XiangpengLiang/Gesture-Interface/guessing.cpp

//#include "window.h"
#include"guessing.h"
#include <QDebug>


guessing::guessing()
{
    paper.load(":/image/paper.png");
    scissor.load(":/image/scissor.png");
    rock.load(":/image/rock.png");
    dog.load(":/image/dog.png");
    boom.load(":/image/boom.png");

    Quit= new QPushButton("Quit", this);
    connect(Quit, SIGNAL (released()), this, SLOT (handleButton()));

}


void guessing::paintEvent(QPaintEvent *)  //Change the picture
{

    QPainter painter(this);


    uint8_t result = Compare[0]<<4|Compare[1]<<3|Compare[2]<<2|Compare[3]<<1|Compare[4];

    switch(result)  //Select picture according to the 5 sensors
    {
    case 0:
    {
        painter.drawPixmap(100,100,500,500,scissor);
        qDebug()<<"scissor";
        break;
    }
    case 19:
    {
        painter.drawPixmap(100,100,500,500,rock);
        qDebug()<<"rock";
        break;
    }
    case 27:
    {
        painter.drawPixmap(100,100,500,500,boom);
        qDebug()<<"boom";
        break;
    }
    case 31:
    {
        painter.drawPixmap(100,100,500,500,paper);
        qDebug()<<"rock";
        break;
    }
    default:
    {
        painter.drawPixmap(100,100,500,500,dog);
        qDebug()<<"dog";
    }
    }
}

void guessing::handleButton(){
    this->close();
}


void guessing::timerEvent( QTimerEvent * )  //Compare and updata the picture every 300ms
{

    for (int i=0;i<5;i++)
        printf("Compare %u = %d  \n", i,Compare[i]);

    static uint8_t result;
    static uint8_t shift;

    result = Compare[0]<<4|Compare[1]<<3|Compare[2]<<2|Compare[3]<<1|Compare[4];

    printf("result = %d  \n\n", result);

    if (result != shift)
    {
        guessing::update();
        shift = result;
        qDebug()<<"Tick";
    }



}


guessing::~guessing()
{


}
